niat-physicalai/esp_watch/asset/breadboard/photo_1.jpeg

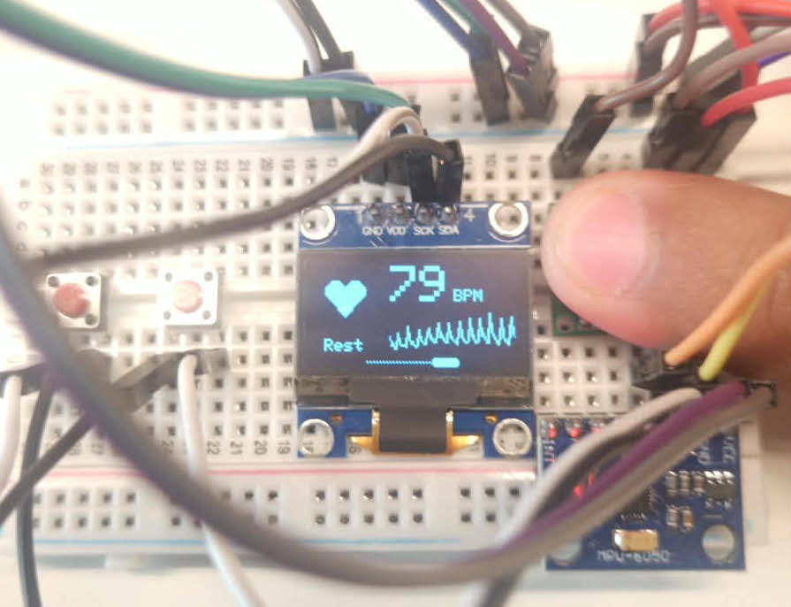
asset/breadboard/photo_1.jpeg
