niat-physicalai/esp_watch/asset/breadboard/photo_2.jpeg

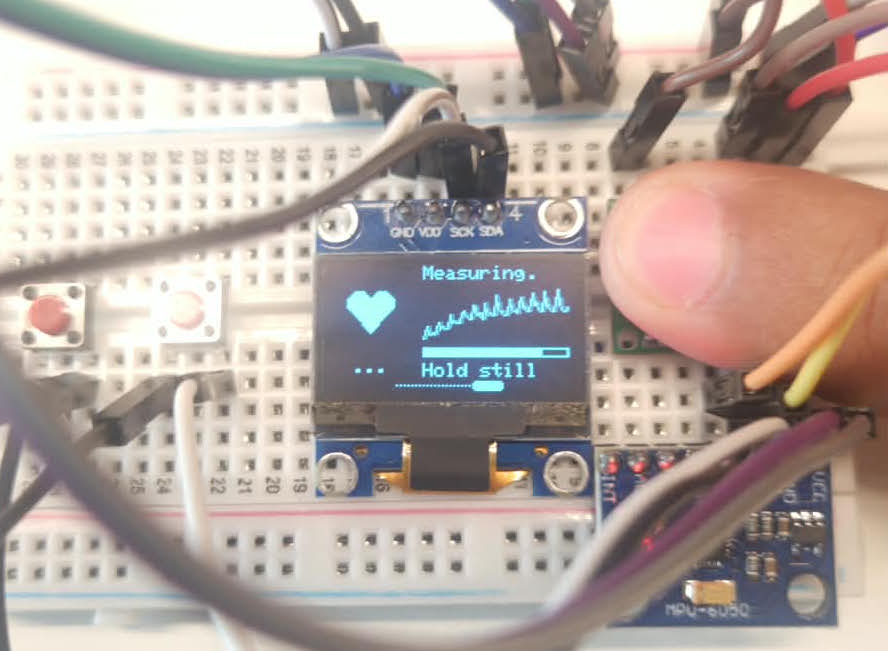
asset/breadboard/photo_2.jpeg
