niat-physicalai/esp_watch/asset/breadboard/photo_3.jpeg

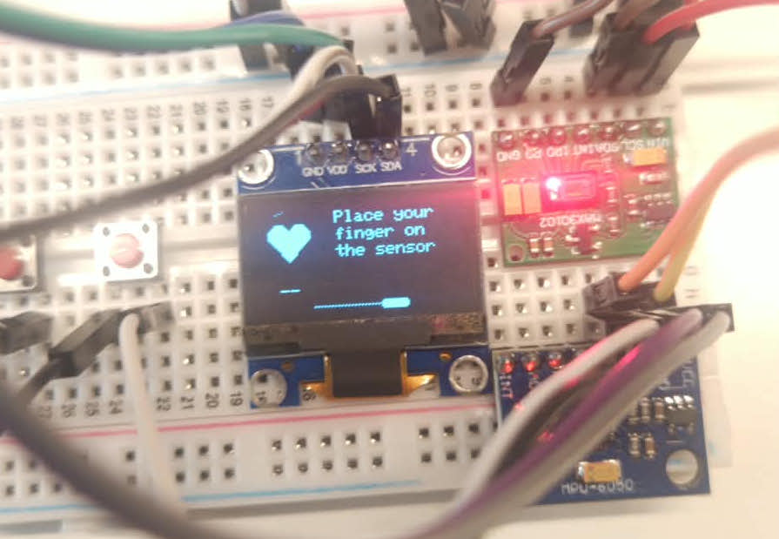
asset/breadboard/photo_3.jpeg
