niat-physicalai/esp_watch/asset/breadboard/photo_4.jpeg

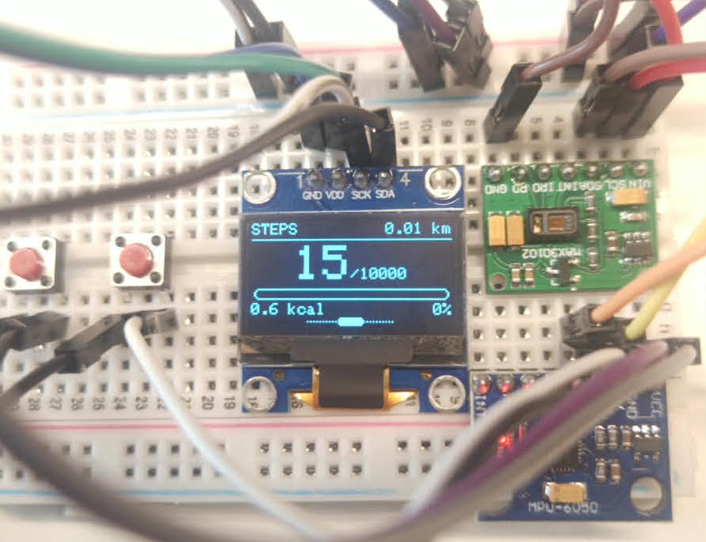
asset/breadboard/photo_4.jpeg
