niat-physicalai/esp_watch/asset/breadboard/photo_5.jpeg

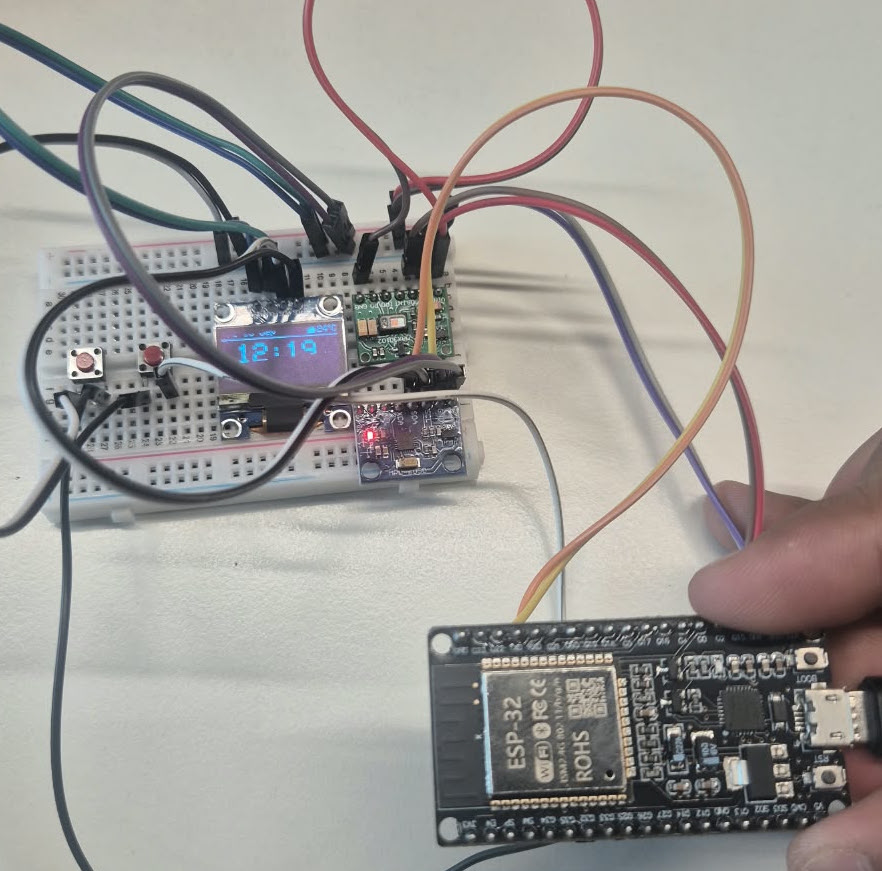
asset/breadboard/photo_5.jpeg
