niat-physicalai/esp_watch/asset/breadboard/photo_6.jpeg

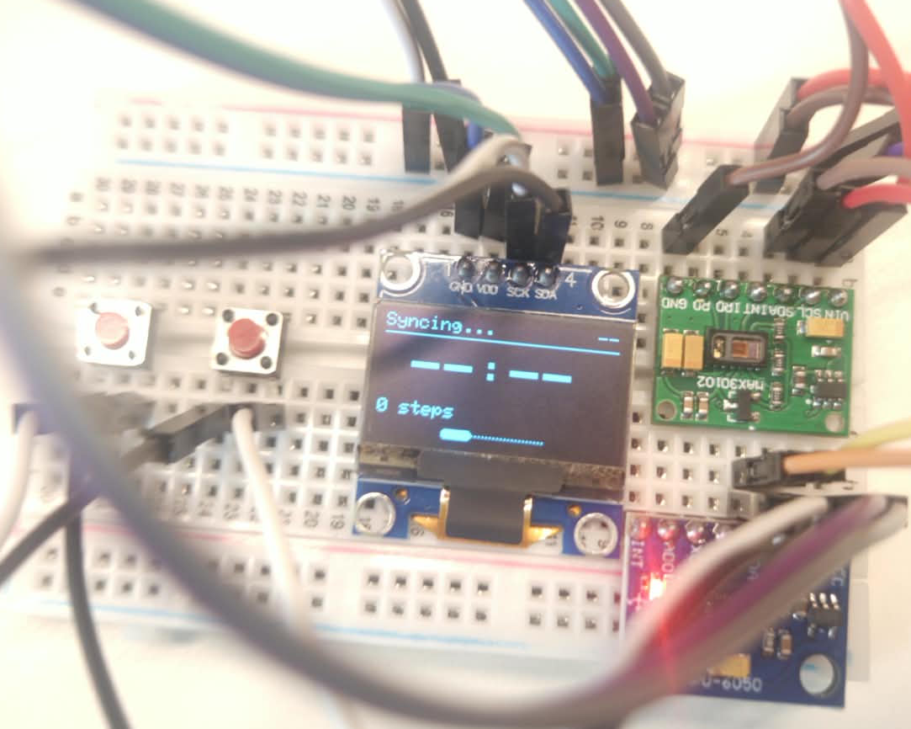
asset/breadboard/photo_6.jpeg
