niat-physicalai/esp_watch/asset/breadboard/photo_7.jpeg

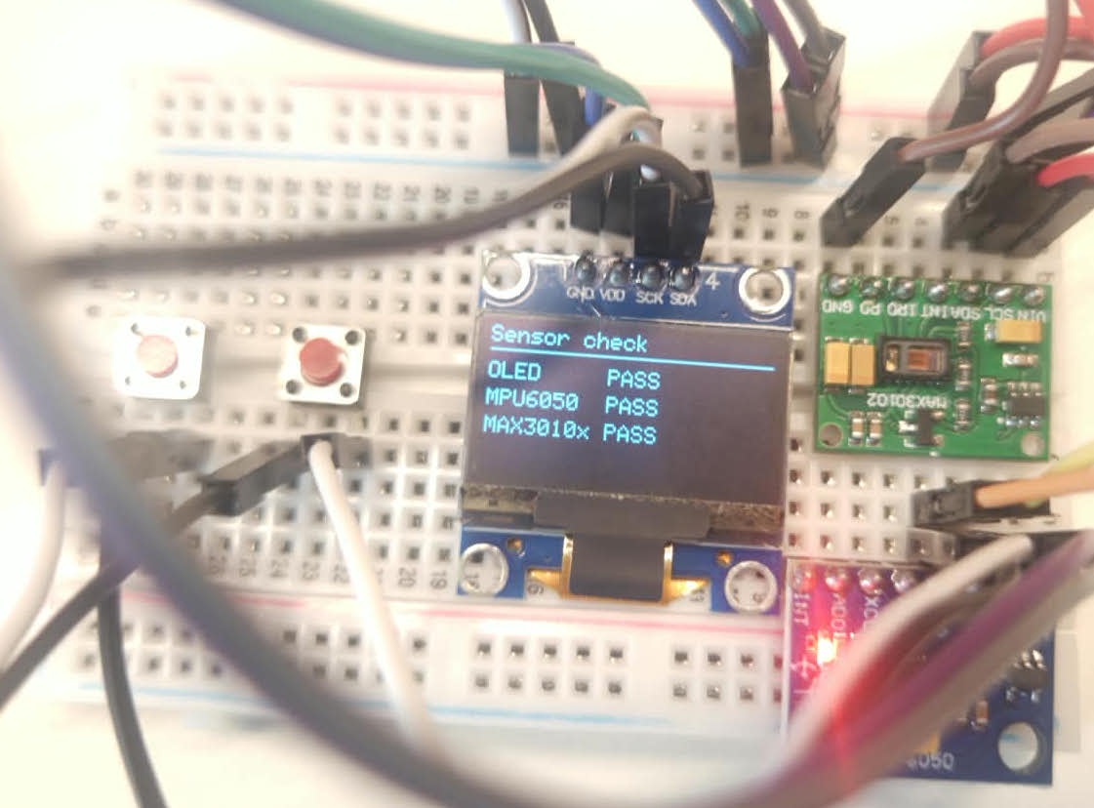
asset/breadboard/photo_7.jpeg
