niat-physicalai/esp_watch/asset/breadboard/photo_8.jpeg

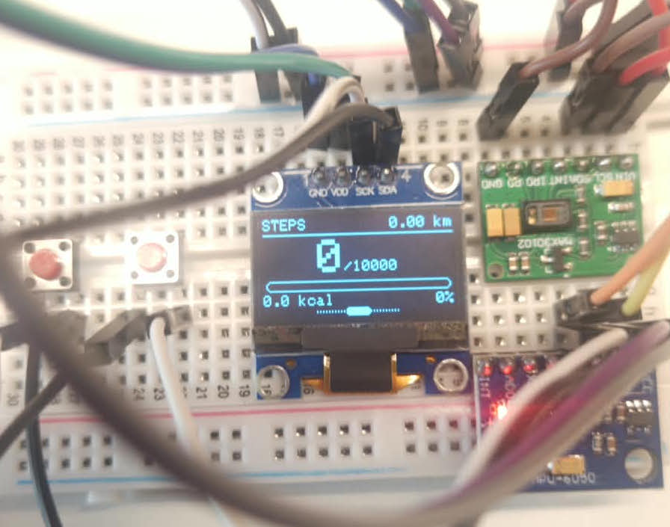
asset/breadboard/photo_8.jpeg
