niat-physicalai/esp_watch/asset/breadboard/photo_10.jpeg

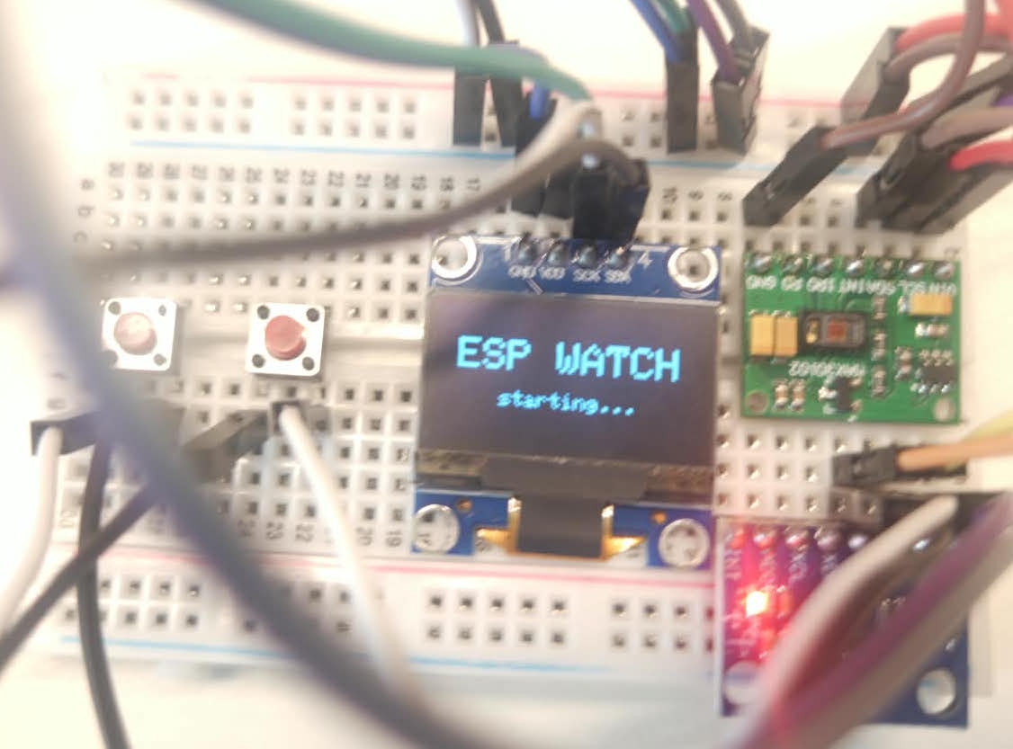
asset/breadboard/photo_10.jpeg
