niat-physicalai/esp_watch/asset/pcb/pcb_front.png

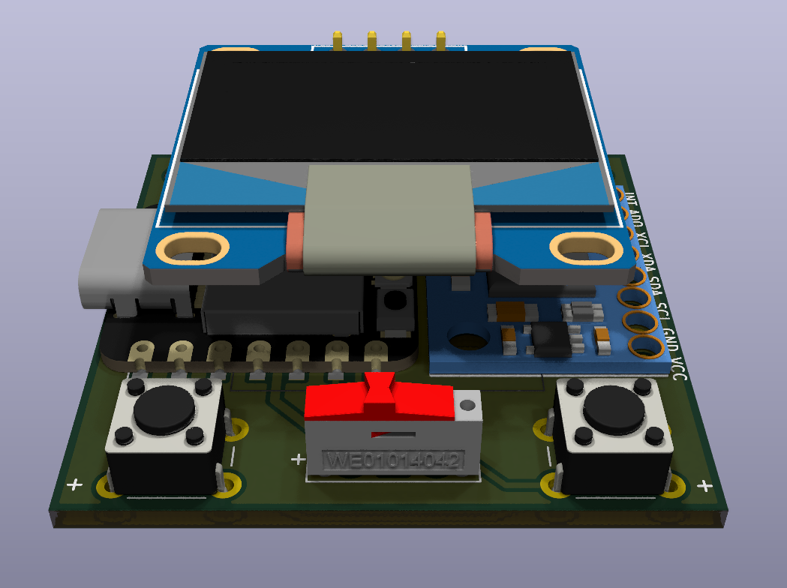
asset/pcb/pcb_front.png
